imyudz/M-dulo-Empilhadeira-Parano-/Apresentações/TELAS ELIPSE/1.png

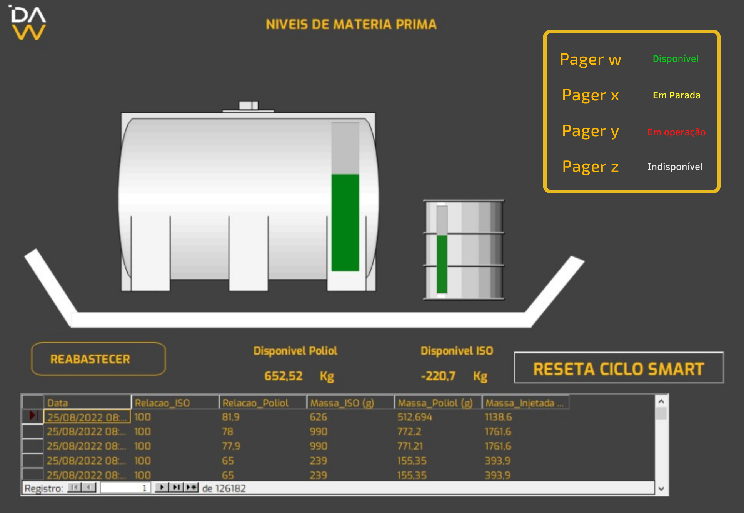
Apresentações/TELAS ELIPSE/1.png
