imyudz/M-dulo-Empilhadeira-Parano-/Apresentações/TELAS ELIPSE/2.png

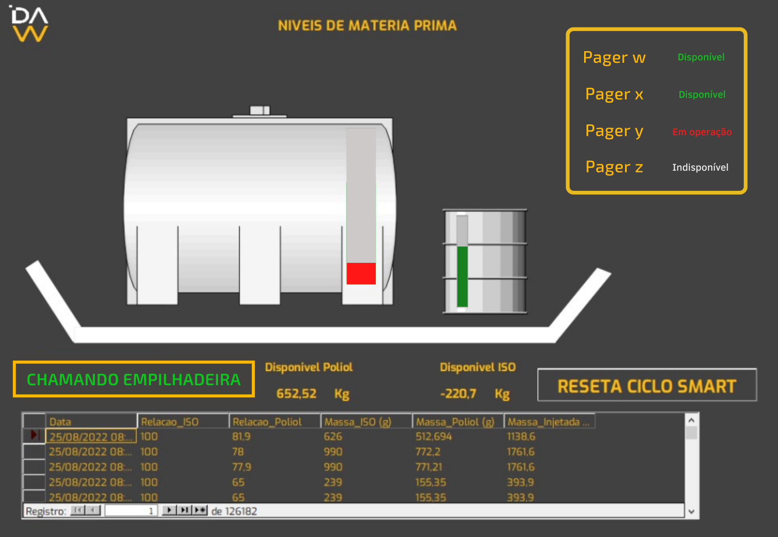
Apresentações/TELAS ELIPSE/2.png
