imyudz/M-dulo-Empilhadeira-Parano-/Apresentações/TELAS ELIPSE/3.png

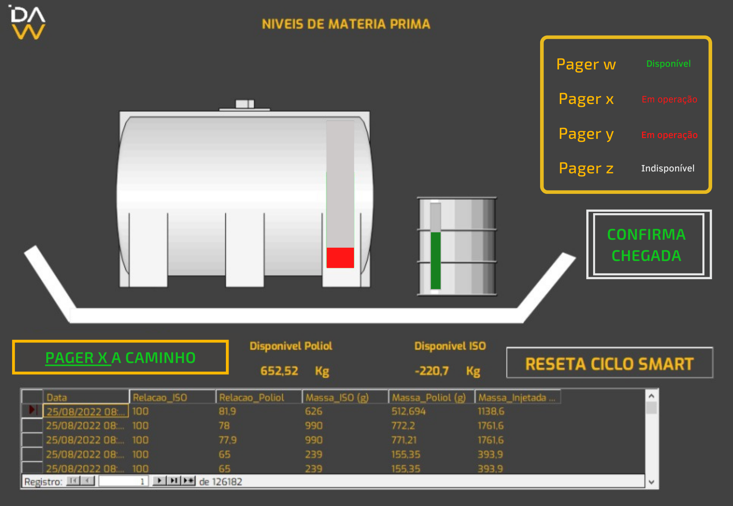
Apresentações/TELAS ELIPSE/3.png
