imyudz/M-dulo-Empilhadeira-Parano-/Apresentações/TELAS ELIPSE/4.png

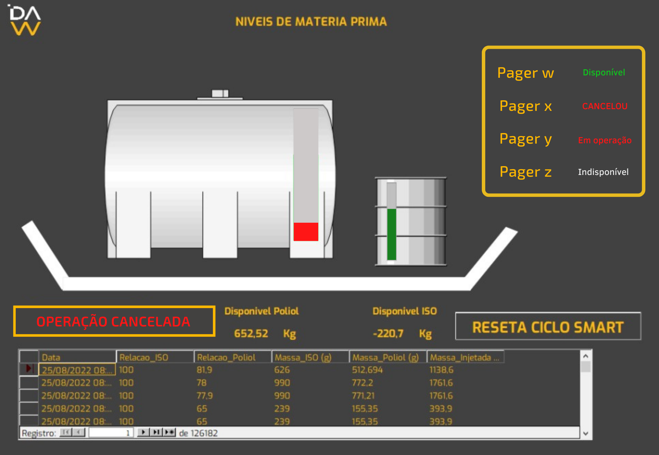
Apresentações/TELAS ELIPSE/4.png
