imyudz/M-dulo-Empilhadeira-Parano-/Apresentações/TELAS ELIPSE/5.png

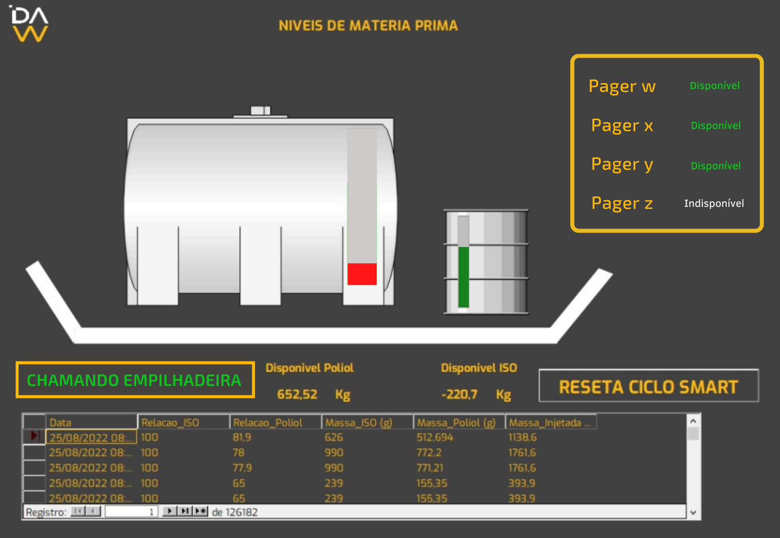
Apresentações/TELAS ELIPSE/5.png
